dJPoida/garage_bot/arduino/garage_bot/botFS.h

/*============================================================================*\
 * Garage Bot - BotFS
 * Peter Eldred 2021-04
 * 
 * File System wrapper for simplifying interactions with LITTLEFS
\*============================================================================*/
#ifndef BOTFS_H
#define BOTFS_H

#include "Arduino.h"

class BotFS {
  public:
    BotFS();
    bool init();
    bool saveConfig();
    void resetWiFiConfig(bool enableWiFi);
    void factoryReset();
    void setWiFiSettings(String newSSID, String newPassword);
    void setIRSensorThreshold(String sensorType, int newThreshold);
    void setGeneralConfig(String mdnsName, String deviceName, bool mqttEnabled, String mqttBrokerAddres, unsigned int mqttBrokerPort, String mqttDeviceId, String mqttUsername, String mqttPassword, String mqttCommandTopic, String mqttStateTopic);
    void registerRFCode(unsigned long newCode);

  private:
    bool loadConfig();

    bool _writingConfig;
};

extern BotFS botFS;

#endif
